promesoft/KicadBerkerPower2/P1040752.JPG

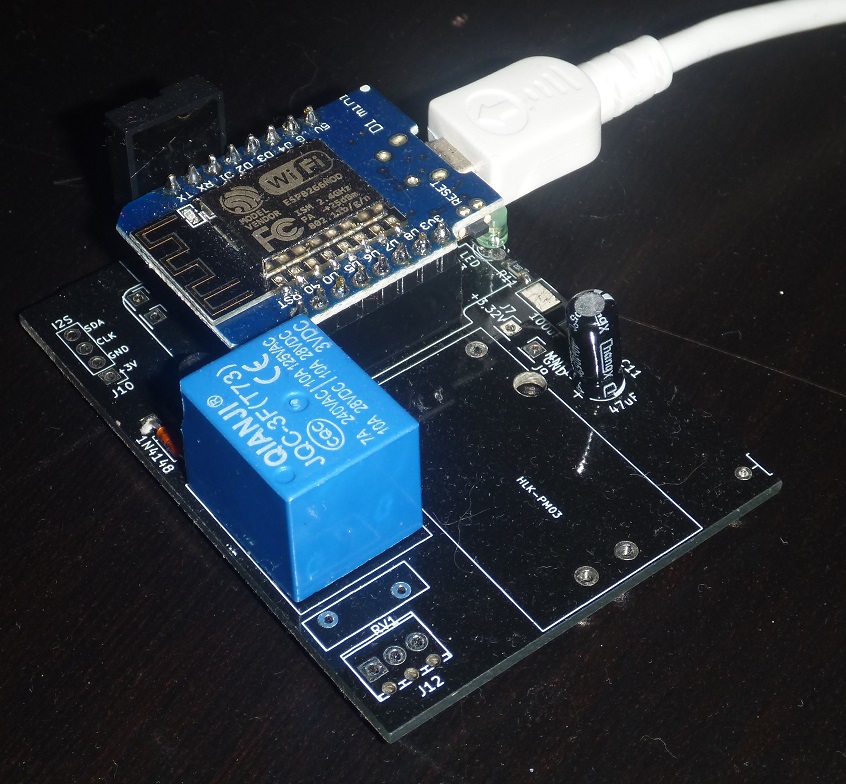
P1040752.JPG
